Iprime111/bluetooth-transmitter/components/oled-display/include/renew_font.h

#ifndef RENEW_FONT_H_
#define RENEW_FONT_H_

// Big thanks to Jared Sanson, who created this font
// Font is taken from https://jared.geek.nz/2014/01/custom-fonts-for-microcontrollers/

#include <stdint.h>

static const uint8_t kFontWidth = 7;

static const uint8_t font[96][7] = {
	{0x00,0x00,0x00,0x00,0x00,0x00,0x00}, //  
	{0x5e,0x00,0x00,0x00,0x00,0x00,0x00}, // !
	{0x0c,0x00,0x0c,0x00,0x00,0x00,0x00}, // "
	{0x14,0x3e,0x14,0x3e,0x14,0x00,0x00}, // #
	{0x2e,0x2a,0x7f,0x2a,0x3a,0x00,0x00}, // $
	{0x1c,0x14,0x1c,0x00,0x7c,0x00,0x70}, // %
	{0x78,0x4e,0x5a,0x2e,0x40,0x00,0x00}, // &
	{0x0c,0x00,0x00,0x00,0x00,0x00,0x00}, // '
	{0x7e,0x81,0x00,0x00,0x00,0x00,0x00}, // (
	{0x81,0x7e,0x00,0x00,0x00,0x00,0x00}, // )
	{0x04,0x1c,0x0e,0x1c,0x04,0x00,0x00}, // *
	{0x08,0x1c,0x08,0x00,0x00,0x00,0x00}, // +
	{0xc0,0x00,0x00,0x00,0x00,0x00,0x00}, // ,
	{0x08,0x08,0x08,0x00,0x00,0x00,0x00}, // -
	{0x40,0x00,0x00,0x00,0x00,0x00,0x00}, // .
	{0x70,0x0e,0x00,0x00,0x00,0x00,0x00}, // /
	{0x7c,0x44,0x7c,0x00,0x00,0x00,0x00}, // 0
	{0x08,0x7c,0x00,0x00,0x00,0x00,0x00}, // 1
	{0x64,0x54,0x4c,0x00,0x00,0x00,0x00}, // 2
	{0x44,0x54,0x7c,0x00,0x00,0x00,0x00}, // 3
	{0x1c,0x10,0x7c,0x00,0x00,0x00,0x00}, // 4
	{0x5c,0x54,0x34,0x00,0x00,0x00,0x00}, // 5
	{0x7c,0x54,0x74,0x00,0x00,0x00,0x00}, // 6
	{0x04,0x04,0x7c,0x00,0x00,0x00,0x00}, // 7
	{0x7c,0x54,0x7c,0x00,0x00,0x00,0x00}, // 8
	{0x1c,0x14,0x7c,0x00,0x00,0x00,0x00}, // 9
	{0x50,0x00,0x00,0x00,0x00,0x00,0x00}, // :
	{0xd0,0x00,0x00,0x00,0x00,0x00,0x00}, // ;
	{0x20,0x50,0x50,0x00,0x00,0x00,0x00}, // <
	{0x28,0x28,0x28,0x00,0x00,0x00,0x00}, // =
	{0x50,0x50,0x20,0x00,0x00,0x00,0x00}, // >
	{0x02,0x5a,0x0e,0x00,0x00,0x00,0x00}, // ?
	{0x7e,0x42,0x5a,0x5a,0x52,0x5e,0x00}, // @
	{0x7e,0x0a,0x0a,0x7e,0x00,0x00,0x00}, // A
	{0x7e,0x4a,0x4a,0x7c,0x00,0x00,0x00}, // B
	{0x7e,0x42,0x42,0x42,0x00,0x00,0x00}, // C
	{0x7e,0x42,0x42,0x7c,0x00,0x00,0x00}, // D
	{0x7e,0x4a,0x4a,0x42,0x00,0x00,0x00}, // E
	{0x7e,0x0a,0x0a,0x02,0x00,0x00,0x00}, // F
	{0x7e,0x42,0x4a,0x7a,0x00,0x00,0x00}, // G
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
};

#endif
